kubajznicek/AdaptBoard-keypad/Adaptboard-models/Body_bottom_cover.stl

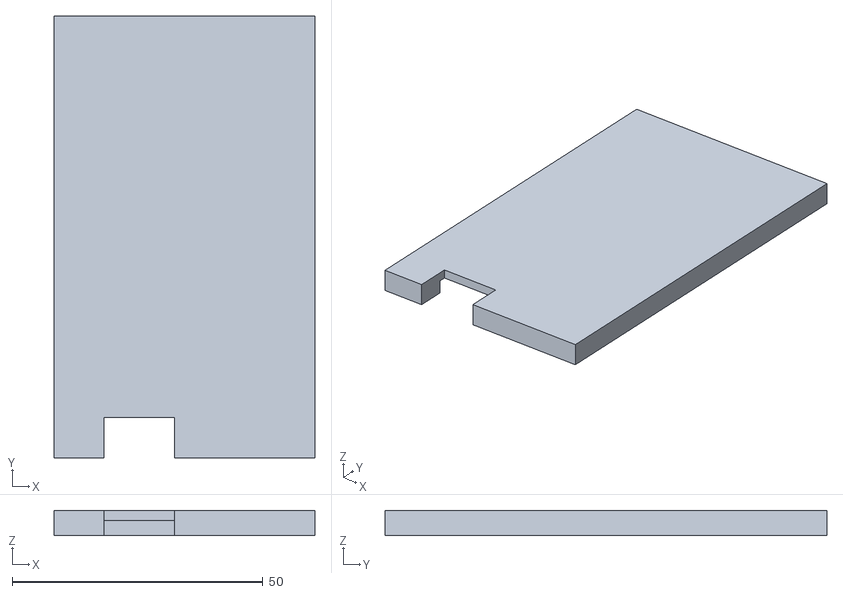
[picture p23: CAD file, 2024-04-18]
Adaptboard-models/Body_bottom_cover.stl
52.0 x 88.0 x 5.00
