kubajznicek/AdaptBoard-keypad/Adaptboard-models/keycaps/keycap_discord_mute.stl

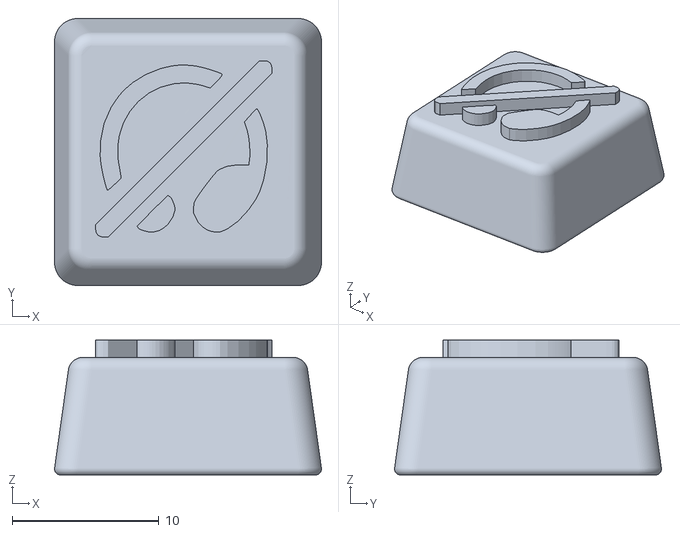
[picture p24: CAD file, 2026-03-02]
Adaptboard-models/keycaps/keycap_discord_mute.stl
18.2 x 18.2 x 9.18
