kubajznicek/AdaptBoard-keypad/Adaptboard-models/keycaps/keycap_sleep.stl

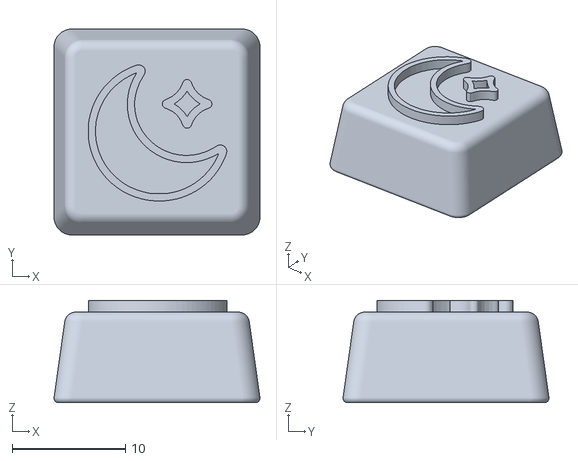
[picture p25: CAD file, 2026-03-02]
Adaptboard-models/keycaps/keycap_sleep.stl
18.2 x 18.2 x 9.04
