kubajznicek/AdaptBoard-keypad/Adaptboard-models/Module_1x1_pot_lid.stl

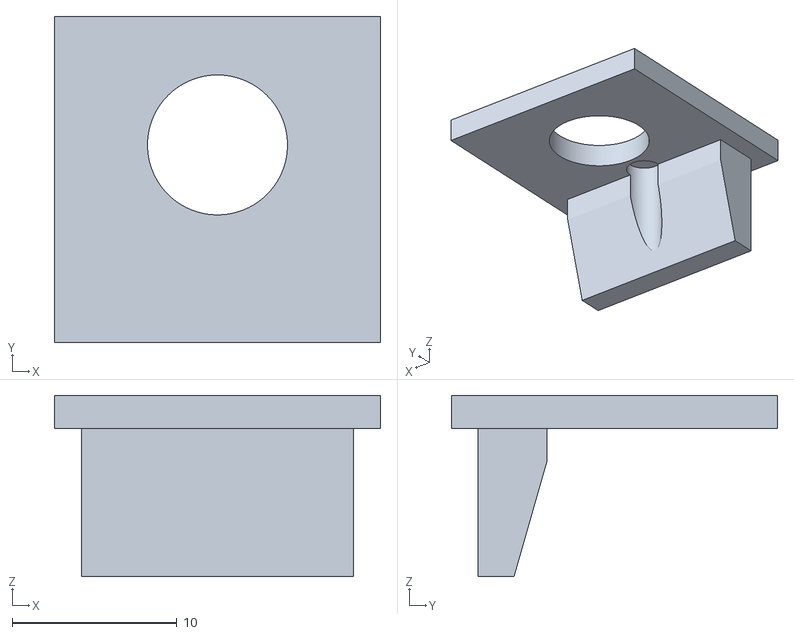
[picture p26: CAD file, 2024-04-18]
Adaptboard-models/Module_1x1_pot_lid.stl
19.8 x 19.8 x 11.0
