kubajznicek/AdaptBoard-keypad/Adaptboard-models/Body_case.stl

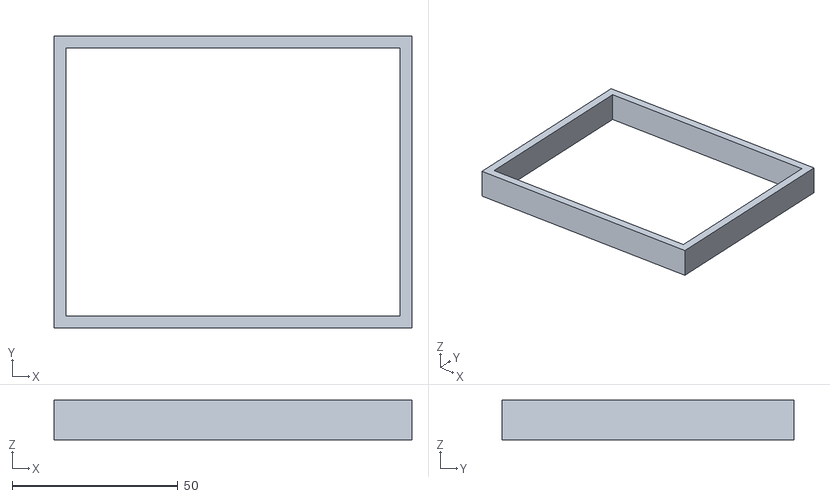
[picture p27: CAD file, 2024-04-18]
Adaptboard-models/Body_case.stl
108.0 x 88.0 x 12.0
