kubajznicek/AdaptBoard-keypad/Adaptboard-models/Module_4x1_slider_lid.stl

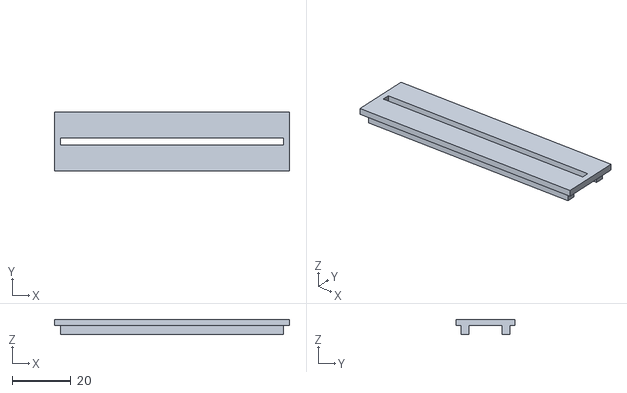
[picture p28: CAD file, 2024-04-18]
Adaptboard-models/Module_4x1_slider_lid.stl
80.0 x 20.0 x 5.00
