kubajznicek/AdaptBoard-keypad/Adaptboard-models/Pot_soldering_holder.stl

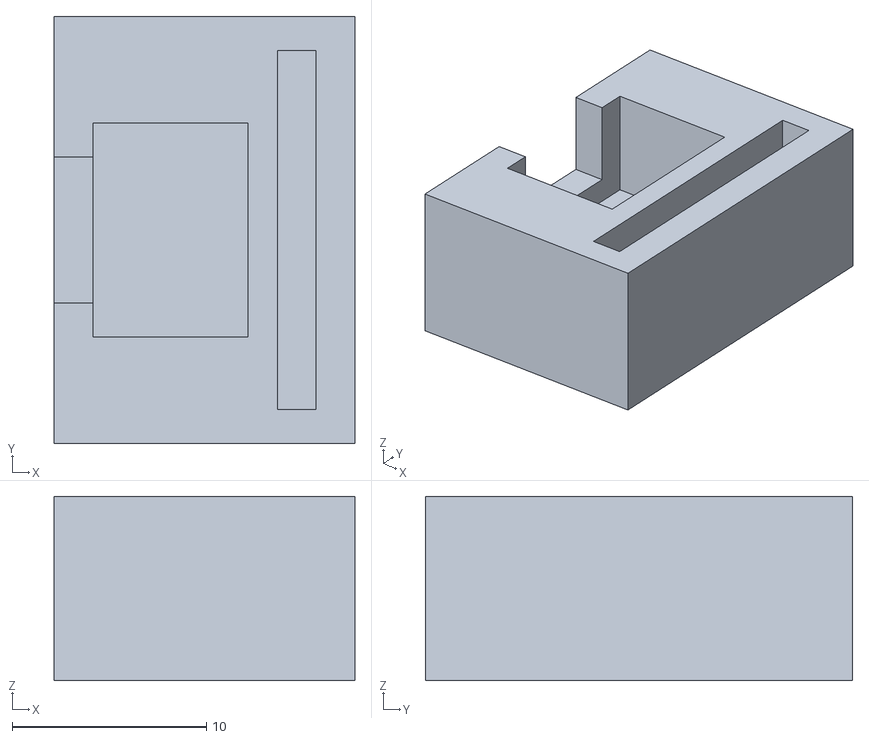
[picture p29: CAD file, 2024-04-18]
Adaptboard-models/Pot_soldering_holder.stl
15.5 x 22.0 x 9.50
