kubajznicek/AdaptBoard-keypad/Adaptboard-models/Body_base.stl

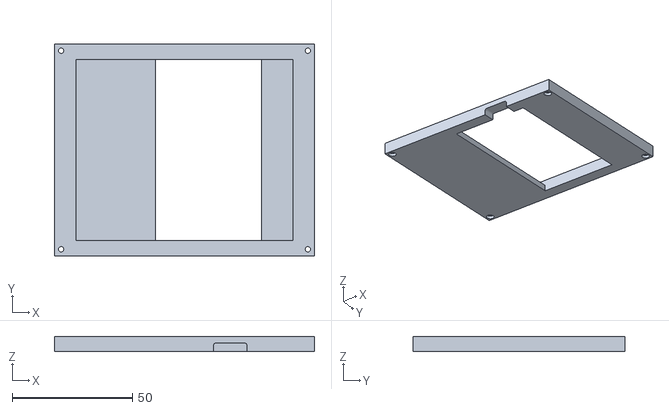
[picture p30: CAD file, 2024-04-18]
Adaptboard-models/Body_base.stl
108.0 x 88.0 x 6.30
